1epaltrik/aicommandos/photos/AICommandos2.jpg

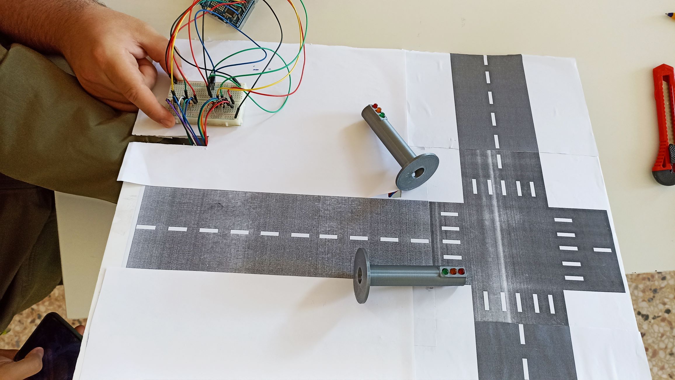
photos/AICommandos2.jpg
