1epaltrik/aicommandos/photos/AICommandos3.jpg

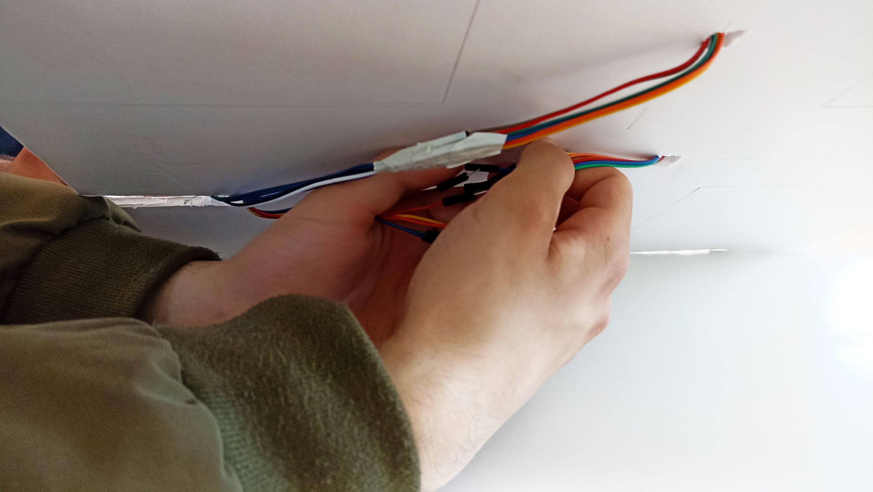
photos/AICommandos3.jpg
