1epaltrik/aicommandos/photos/AICommandos4.jpg

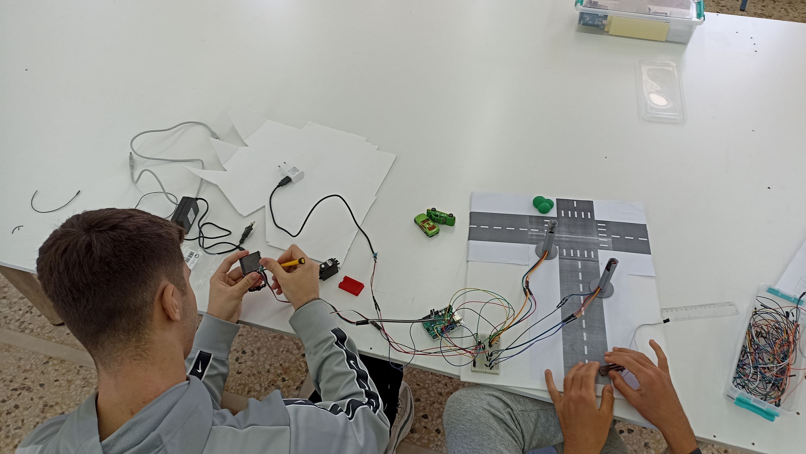
photos/AICommandos4.jpg
