1epaltrik/aicommandos/photos/AICommandos6.jpg

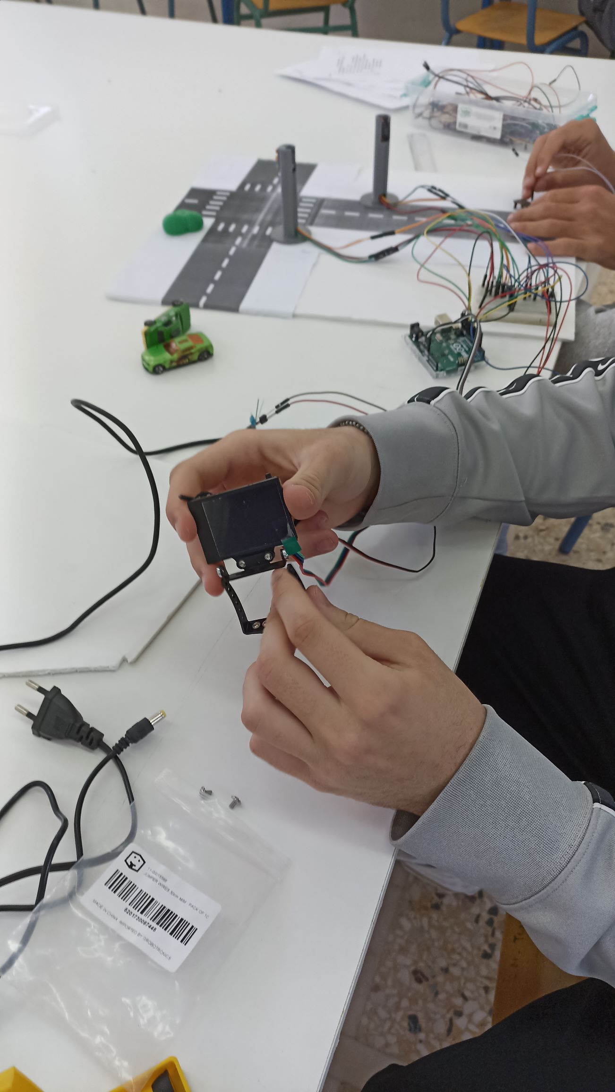
photos/AICommandos6.jpg
