1epaltrik/aicommandos/photos/AICommandos8.jpg

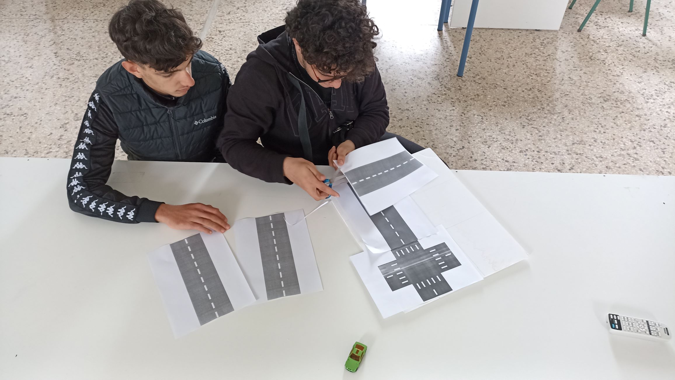
photos/AICommandos8.jpg
