1epaltrik/aicommandos/photos/AICommandos9.jpg

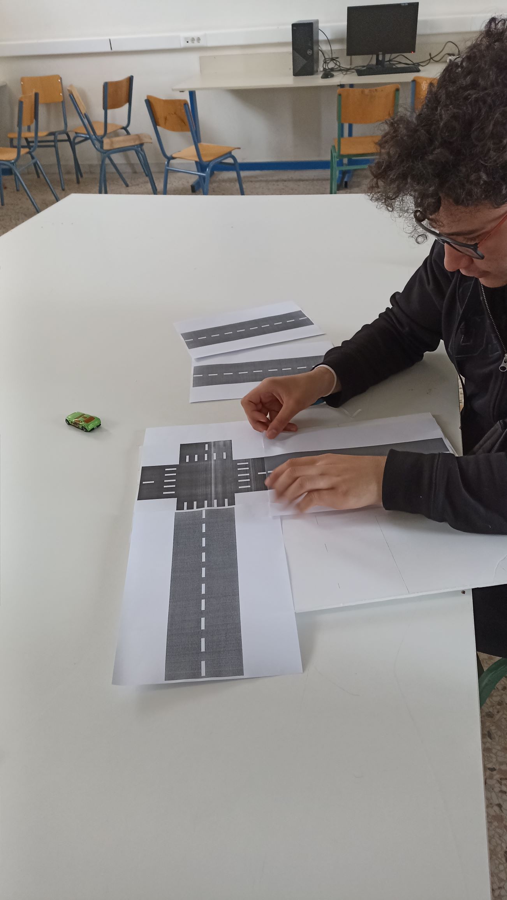
photos/AICommandos9.jpg
