1epaltrik/aicommandos/photos/AICommandos10.jpg

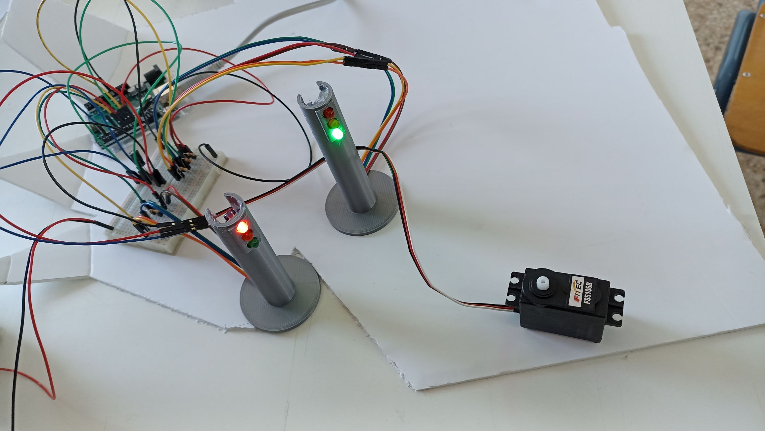
photos/AICommandos10.jpg
