1epaltrik/aicommandos/photos/AICommandos11.jpg

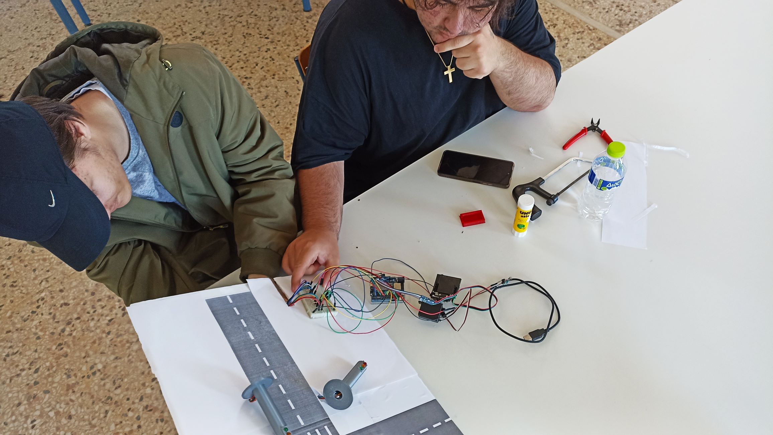
photos/AICommandos11.jpg
