1epaltrik/aicommandos/photos/presentations/gisemi1.jpg

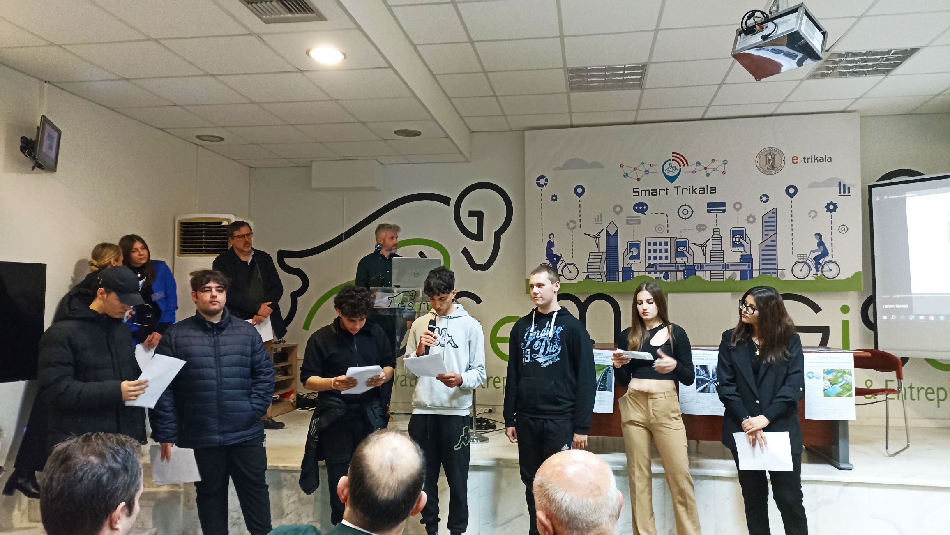
photos/presentations/gisemi1.jpg
