1epaltrik/aicommandos/photos/presentations/gisemi3.jpg

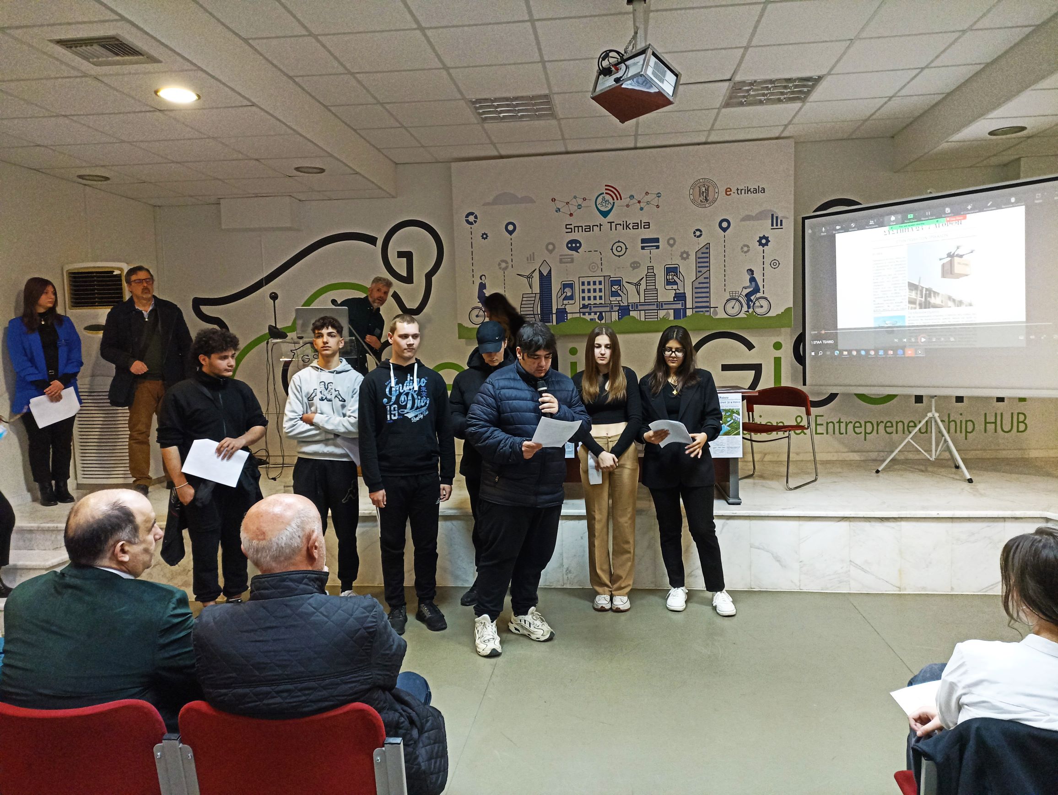
photos/presentations/gisemi3.jpg
