1epaltrik/aicommandos/photos/presentations/gisemi4.jpg

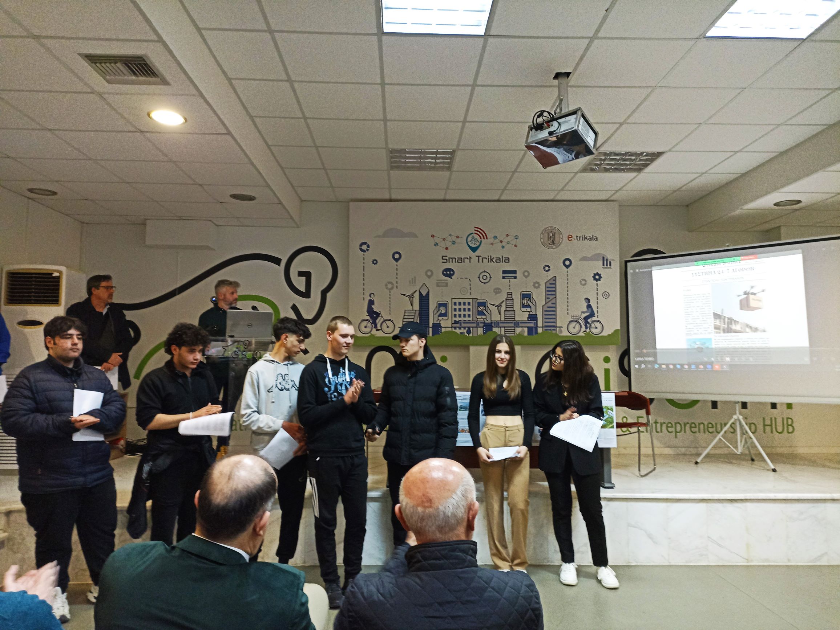
photos/presentations/gisemi4.jpg
