1epaltrik/aicommandos/photos/presentations/Thetalos1.jpg

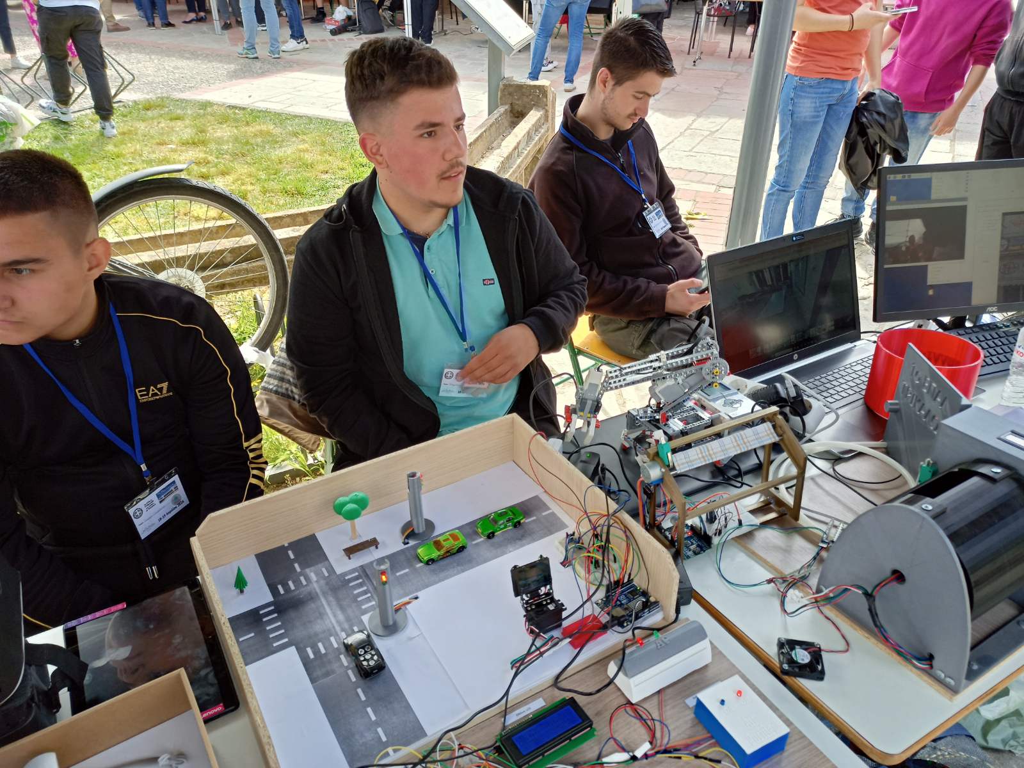
photos/presentations/Thetalos1.jpg
