1epaltrik/aicommandos/photos/presentations/Thetalos2.jpg

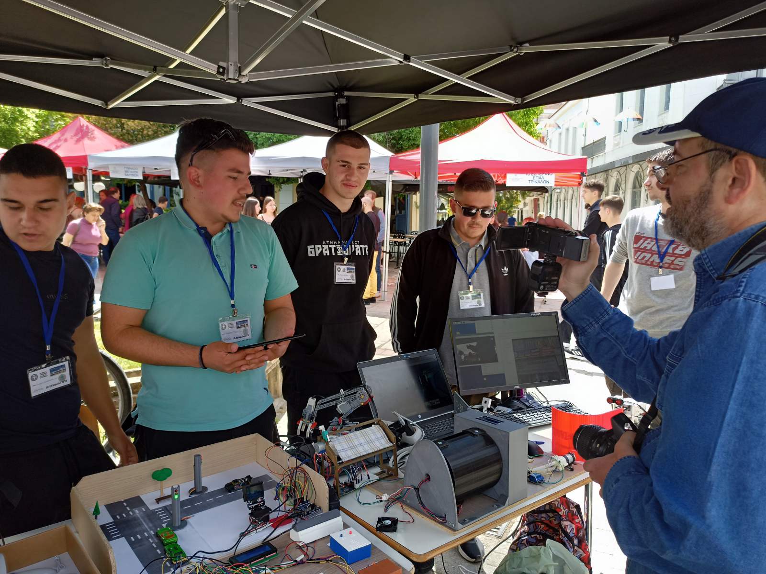
photos/presentations/Thetalos2.jpg
